BruceFletcher/SpaceTime/hw/Display.sch

## KiCad design hw/Display.sch (2013-02-14)

Schematic: Display.sch

Parts:
7S-1, 7S-2, 7S-3, 7S-4: NFD-23011Ax-11
Extra1, Extra2, Extra3, Extra4: CONN_1
P1: Main board
R1, R2, R3, R4, R5, R6, R7, R8, R9, R10, R11, R12, R13, R14, R15, R16, R17, R18, R19, R20, R21, R22, R23, R24, R25, R26, R27, R28: x Ω
R29, R30, R31, R32: y Ω
