BruceFletcher/SpaceTime/hw/Drivers.sch

## KiCad design hw/Drivers.sch (2013-05-21)

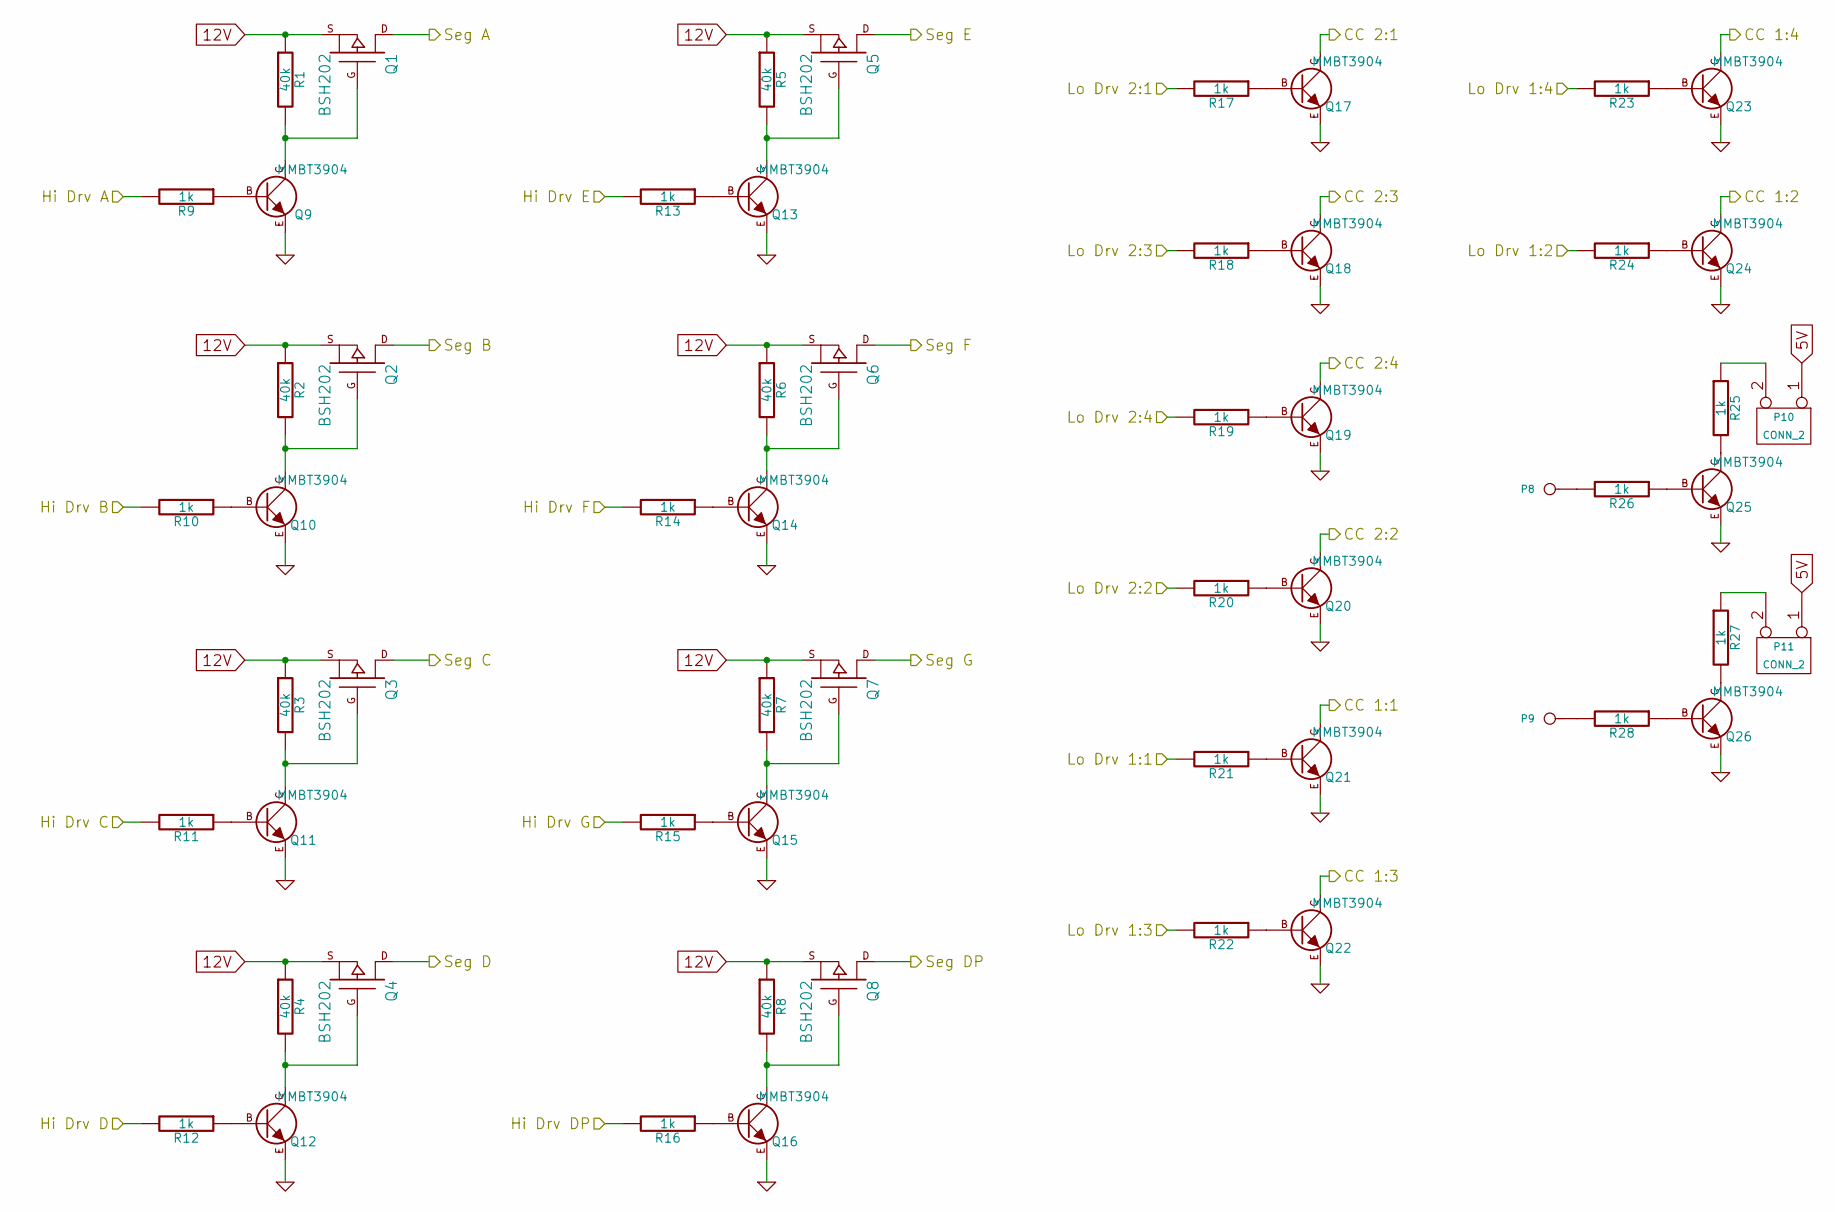
[picture p4: schematic Drivers.sch]

Parts:
P8, P9: CONN_1
P10, P11: CONN_2
Q1, Q2, Q3, Q4, Q5, Q6, Q7, Q8: BSH202
Q9, Q10, Q11, Q12, Q13, Q14, Q15, Q16, Q17, Q18, Q19, Q20, Q21, Q22, Q23, Q24, Q25, Q26: MMBT3904; TO92-EBC
R1, R2, R3, R4, R5, R6, R7, R8: 40k
R9, R10, R11, R12, R13, R14, R15, R16, R17, R18, R19, R20, R21, R22, R23, R24, R25, R26, R27, R28: 1k

Connections:
5V: P10.1, P11.1
12V: Q1.S, Q2.S, Q3.S, Q4.S, Q5.S, Q6.S, Q7.S, Q8.S, R1.1, R2.1, R3.1, R4.1, R5.1, R6.1, R7.1, R8.1
CC 1:1: Q21.C
CC 1:2: Q24.C
CC 1:3: Q22.C
CC 1:4: Q23.C
CC 2:1: Q17.C
CC 2:2: Q20.C
CC 2:3: Q18.C
CC 2:4: Q19.C
GND: Q9.E, Q10.E, Q11.E, Q12.E, Q13.E, Q14.E, Q15.E, Q16.E, Q17.E, Q18.E, Q19.E, Q20.E, Q21.E, Q22.E, Q23.E, Q24.E, Q25.E, Q26.E
Hi Drv A: R9.2
Hi Drv B: R10.2
Hi Drv C: R11.2
Hi Drv D: R12.2
Hi Drv DP: R16.2
Hi Drv E: R13.2
Hi Drv F: R14.2
Hi Drv G: R15.2
Lo Drv 1:1: R21.2
Lo Drv 1:2: R24.2
Lo Drv 1:3: R22.2
Lo Drv 1:4: R23.2
Lo Drv 2:1: R17.2
Lo Drv 2:2: R20.2
Lo Drv 2:3: R18.2
Lo Drv 2:4: R19.2
unnamed: P8.1, R26.2
unnamed: P9.1, R28.2
unnamed: P10.2 (PM), R25.1
unnamed: P11.2 (PM), R27.1
unnamed: Q1.G, Q9.C, R1.2
unnamed: Q9.B, R9.1
unnamed: Q10.B, R10.1
unnamed: Q2.G, Q10.C, R2.2
unnamed: Q11.B, R11.1
unnamed: Q3.G, Q11.C, R3.2
unnamed: Q12.B, R12.1
unnamed: Q4.G, Q12.C, R4.2
unnamed: Q13.B, R13.1
unnamed: Q5.G, Q13.C, R5.2
unnamed: Q14.B, R14.1
unnamed: Q6.G, Q14.C, R6.2
unnamed: Q15.B, R15.1
unnamed: Q7.G, Q15.C, R7.2
unnamed: Q16.B, R16.1
unnamed: Q8.G, Q16.C, R8.2
unnamed: Q17.B, R17.1
unnamed: Q18.B, R18.1
unnamed: Q19.B, R19.1
unnamed: Q20.B, R20.1
unnamed: Q21.B, R21.1
unnamed: Q22.B, R22.1
unnamed: Q23.B, R23.1
unnamed: Q24.B, R24.1
unnamed: Q25.B, R26.1
unnamed: Q25.C, R25.2
unnamed: Q26.B, R28.1
unnamed: Q26.C, R27.2
Seg A: Q1.D
Seg B: Q2.D
Seg C: Q3.D
Seg D: Q4.D
Seg DP: Q8.D
Seg E: Q5.D
Seg F: Q6.D
Seg G: Q7.D
