BruceFletcher/SpaceTime/hw/SpaceTime.sch

## KiCad design hw/SpaceTime.sch (2013-05-21)

Schematic: SpaceTime.sch

Parts:
A5, A6, A11, A12, A13, A14: CONN_1
Aref1: CONN_1
C1, C2, C3, C10, C11, C12: 0.1uF
C4, C5: 22pf
C6, C7: 10uF
D1: DIODESCH
D2: Power
Extra1, Extra2, Extra3, Extra4, Extra5, Extra6, Extra7, Extra8: CONN_1
G1: CONN_1
J1: JACK_2P
Ja1, Ja2, Ja3: CONN_1
M1, M2, M3, M4: MOUNTING_HOLE
MCU1: ATMEGA328P-P; DIL28
P1: AVR-ISP; AVR-ISP-6
P2: Serial
P3: Current time
P4: Closing time
P6: SPK
P7: Keyboard
Q29: BSH202,215
Q30: MMBT3904; TO92-EBC
R29, R31, R32: 10k
R30: 150
R34: 40k
R35: 1k
RX1: CONN_1
SER1, SER2, SER3, SER4, SER5, SER6: CONN_1
SW1: Reset
Sout-1: CONN_1
TX1: CONN_1
U1: LM7805
U2, U3: 74HC595
V1: CONN_1
XTL1: 14.7456MHz
