BruceFletcher/SpaceTime/sw/display.c

/**
 * Display functions for SpaceTime project
 */

#include <stdio.h>
#include <string.h>
#include "timer.h"
#include "shift.h"
#include "keypad.h"
#include "display.h"
#include "watchdog.h"


/**
 * Running full out, the high-side mosfet drivers aren't able to turn off quickly enough.
 * The result is 'off' segments that look half-on.  Slowing down the scanning rate by
 * a factor of 32 doesn't seem to introduce any significant flicker to the display, but
 * does allow the off segments to look more like they're off.  Good enough.
 */
#if 1
#define SLOW_LOOP
#endif


#define display_separator_blink(s) ((s)==DISPLAY_SEPARATOR_BLINK ? 1 : 0)
#define display_separator_mask(s, mask) ((s)!=DISPLAY_SEPARATOR_OFF ? (mask) : 0)


/**
 * This is set from main() (or somewhere else) to indicate what characters to display.
 */
display_row_t display_buffer[DISPLAY_ROW_COUNT];

/**
 * This is the copy of the above structure that we're currently scanning out.
 */
static display_row_t current_display[DISPLAY_ROW_COUNT];

/**
 * Bytes that are actually sent out for digit selector value during display updates.
 *
 * Subscripts are:
 *
 * 2 - alternate views updated once per second, using timer.h's current_time.ts.second
 * 4 - A loop of 4 states, for brightness control (just cycled, POV-style)
 * 8 - Per-segment selector for which digits to enable
 */
typedef unsigned char output_state_t[4][8];

static output_state_t output_buffer[2];

/**
 * Counter for brightness control, should be 0-3, updated after each loop through 8 segments
 */
static unsigned char digit_brightness_counter;

/**
 * This loops 0-7 to drive segments.  In the 0-3 range it also drives the keypad.
 */
static unsigned char segment_loop_counter;

/**
 * Segments to enable for each given type of character to be displayed.
 *
 * The order of these character mappings must match enum values in display_char_t.
 */
static const unsigned char character_map[] =
{
  0x3f,  // 0
  0x06,  // 1
  0x5b,  // 2
  0x4f,  // 3
  0x66,  // 4
  0x6d,  // 5
  0x7c,  // 6
  0x07,  // 7
  0x7f,  // 8
  0x67,  // 9
  0x00,  // space
  0x08,  // underscore
  0x40,  // dash
  0x6d,  // S
  0x76   // H
};


/**
 * Called from main() upon system startup.
 */
void display_init()
{
  shift_out(0, 0);

#ifdef SLOW_LOOP
  segment_loop_counter = -1;
#endif
  digit_brightness_counter = -1;

  memset(display_buffer, 0, sizeof(display_buffer));
  memset(output_buffer, 0, sizeof(output_buffer));
}


/**
 * Initialize a two-row display buffer.
 *
 * Everything is set to a constant brightness, with no blinking.
 */
void display_buffer_initialize(display_row_t *buffer, char brightness)
{
  unsigned char row, digit;

  memset(buffer, 0, sizeof(display_row_t)*2);

  for (row=0; row<2; ++row)
  {
    for (digit=0; digit<4; ++digit)
    {
      buffer[row].digit[digit].brightness[0]=brightness;
      buffer[row].digit[digit].brightness[1]=brightness;
    }
  }
}


/**
 * Clear a display buffer row.
 *
 * Sets all four digits of one display row to blanks.
 */
void display_buffer_clear_row(display_row_t *buffer)
{
  unsigned char digit;

  for (digit=0; digit<4; ++digit)
    buffer->digit[digit].value = DISPLAY_CHAR_SPACE;
}


/**
 * Per-digit brightness is implemented by duplicating digits through up to 4 per-segment
 * digit buffers; essentially a static POV system.
 *
 * Output state 0 is already filled in, we need to copy states 1-3 based on
 * display_buffer[row].digit[n].brightness[brightness_index].
 */
static void do_brightness_duplications(output_state_t *buffer, unsigned char brightness_index)
{
  unsigned char cycle, row, digit, segment, mask;

  for (cycle=1; cycle<4; ++cycle)
  {
    mask = 0;

    for (row=0; row<2; ++row)
    {
      for (digit=0; digit<4; ++digit)
      {
        if (current_display[row].digit[digit].brightness[brightness_index] >= cycle)
          mask |= (1<<(row*4+digit));
      }
    }

    for (segment=0; segment<8; ++segment)
    {
      (*buffer)[cycle][segment] = (*buffer)[0][segment] & mask;
    }
  }
}

/**
 * Set a segment in the output buffer to a given brightness and blink value.
 *
 * This can be used to override a segment (e.g. for underbar) or add decimal
 * points for min:sec separation.  Or anything, really.
 */
static void stuff_segment(unsigned char segment, char blink, char brightness, unsigned char digit_mask)
{
  unsigned char blink_cycle, brightness_cycle, mask;

  for (blink_cycle=0; blink_cycle<2; ++blink_cycle)
  {
    if (blink_cycle==0 || !blink)
      mask = digit_mask;
    else
      mask = 0;

    for (brightness_cycle=0; brightness_cycle<4; ++brightness_cycle)
    {
      if (mask && brightness_cycle < brightness)
        output_buffer[blink_cycle][brightness_cycle][segment] |= digit_mask;
      else
        output_buffer[blink_cycle][brightness_cycle][segment] &= ~digit_mask;
    }
  }
}

/**
 * Called from display_update() whenever a change is made to the display_buffer.
 *
 * This function pre-calculates an array of bytes that are shifted out for the
 * digit selector value on each display_update() call.
 */
static void update_digit_sequence()
{
  unsigned char row, digit, segment, character, d_mask, blink;

  memset(output_buffer, 0, sizeof(output_buffer));
  memcpy(current_display, display_buffer, sizeof(current_display));

  for (row=0; row<2; ++row)
  {
    for (digit=0; digit<4; ++digit)
    {
      character = character_map[display_buffer[row].digit[digit].value];
      d_mask = (1 << (row*4+digit));

      for (segment=0; segment<7; ++segment)
      {
        if (character & (1<<segment))
          output_buffer[0][0][segment] |= d_mask;
      }
    }
  }

  // For per-second blinking, first lighting sequence is essentially the same.
  memcpy(&output_buffer[1][0], &output_buffer[0][0], 8*sizeof(char));

  // Copy the segment/digit data up to 3 times to set the brightness.
  do_brightness_duplications(&output_buffer[0], 0);  // blink state 0
  do_brightness_duplications(&output_buffer[1], 1);  // blink state 1

  // Set up mm:ss separators for time display.
  blink = display_separator_blink(current_display[0].separator);
  d_mask = display_separator_mask(current_display[0].separator, 0x06);
  stuff_segment(7,        // segment (7=decimal point)
                blink,    // blink (0/1)
                4,        // brightness, 0-4
                d_mask);  // digit mask

  blink = display_separator_blink(current_display[1].separator);
  d_mask = display_separator_mask(current_display[1].separator, 0x60);
  stuff_segment(7,        // segment (7=decimal point)
                blink,    // blink (0/1)
                4,        // brightness, 0-4
                d_mask);  // digit mask

  for (row=0; row<2; ++row)
  {
    for (digit=0; digit<4; ++digit)
    {
      if (current_display[row].digit[digit].underbar)
      {
        d_mask = (1<<(row*4+digit));
        stuff_segment(3,        // segment (3=segment D, bottom)
                      1,        // blink (0/1)
                      4,        // brightness, 0-4
                      d_mask);  // digit mask
      }
    }
  }
}

/**
 * Called from main() repeatedly to drive the display.
 *
 * Segments are scanned in a steady 0-7 loop, and digits are enabled/disabled
 * according to character, intensity, cursor, blink, etc.
 */
void display_update()
{
  static unsigned char last_segment;
  unsigned char segment;
  unsigned char digit;
  unsigned char tick;
#ifdef SLOW_LOOP
  unsigned char keyscan;
  static unsigned char last_keyscan = 255;
#endif

  if (memcmp(display_buffer, current_display, sizeof(display_buffer)))
    update_digit_sequence();

#ifdef SLOW_LOOP
  ++segment_loop_counter;

  if (++digit_brightness_counter > 31)
    digit_brightness_counter = 0;
#else
  if (++segment_loop_counter > 7)
    segment_loop_counter = 0;

  if (++digit_brightness_counter > 3)
    digit_brightness_counter = 0;
#endif

  tick = current_time.ts.second & 1;

#ifdef SLOW_LOOP
  segment = (1<<(segment_loop_counter>>5));
  digit = output_buffer[tick][digit_brightness_counter>>3][segment_loop_counter>>5];
#else
  segment = (1<<segment_loop_counter);
  digit = output_buffer[tick][digit_brightness_counter][segment_loop_counter];
#endif

  shift_out(digit, segment);

  /*
   * If the segment is regularly updating, we can safely enable the shift registers
   * and tell the watchdog timer to restart its count.  This allows us to overdrive
   * the display with more confidence that some firmware screwup isn't going to
   * cook the display by sticking on one segment or another.
   */
  if (segment != last_segment)
  {
    last_segment = segment;
    watchdog_tick();
    shift_output_enable(1, 1);
  }

#ifdef SLOW_LOOP
  keyscan = segment_loop_counter>>5;
  if (keyscan != last_keyscan && keyscan < 4)
  {
    last_keyscan = keyscan;
    keypad_scan(keyscan);
  }
#else
  if (segment_loop_counter < 4)
    keypad_scan(segment_loop_counter);
#endif
}
